ccg-esb-lab/BAFFLE/data/Figure_gradient/gradMontage_small.png

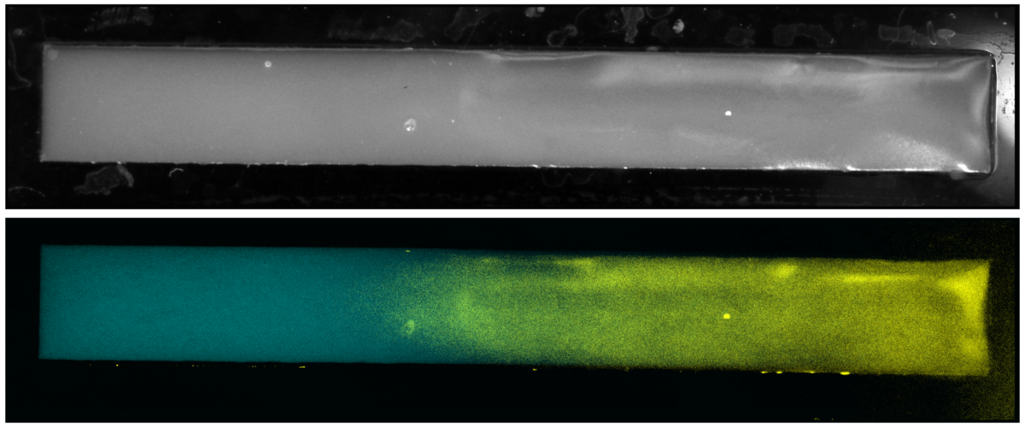
data/Figure_gradient/gradMontage_small.png
