ccg-esb-lab/BAFFLE/data/Figure_gradient/gradComposite.png

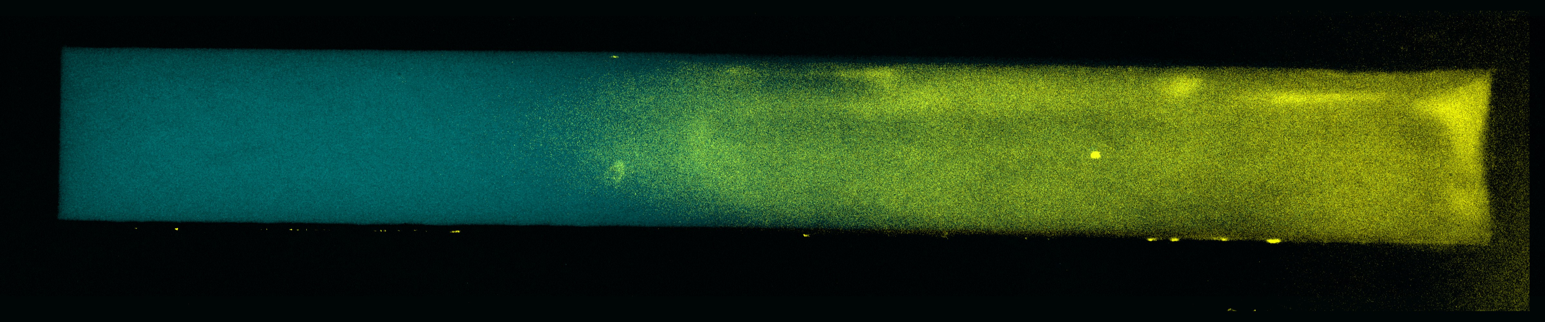
data/Figure_gradient/gradComposite.png
