ccg-esb-lab/BAFFLE/data/Figure_colonies/IMG_0024.JPG

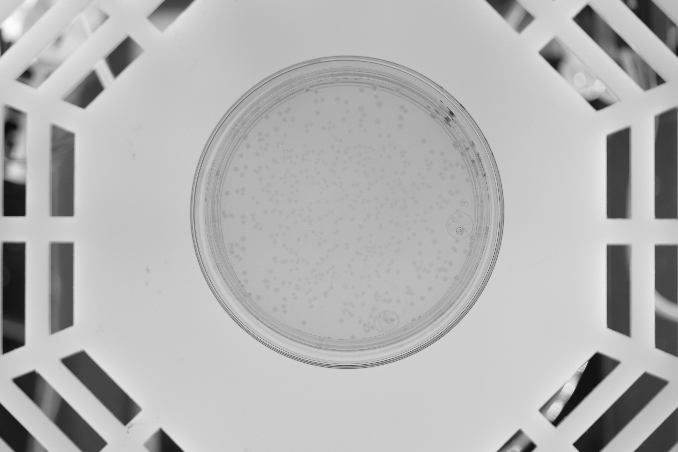
data/Figure_colonies/IMG_0024.JPG
