ccg-esb-lab/BAFFLE/data/Figure_colonies/IMG_0025.JPG

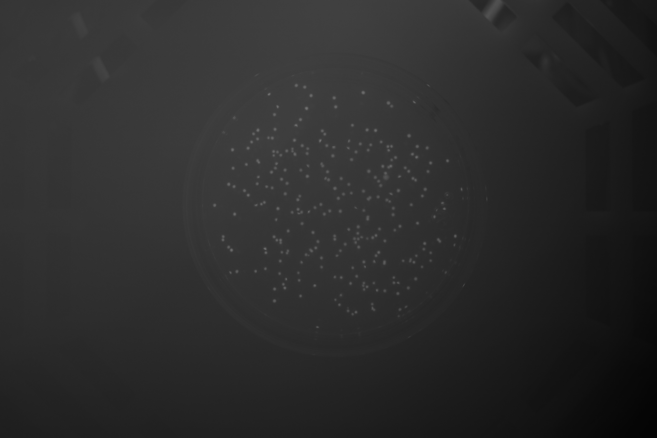
data/Figure_colonies/IMG_0025.JPG
