ccg-esb-lab/BAFFLE/data/Figure_colonies/IMG_0036.JPG

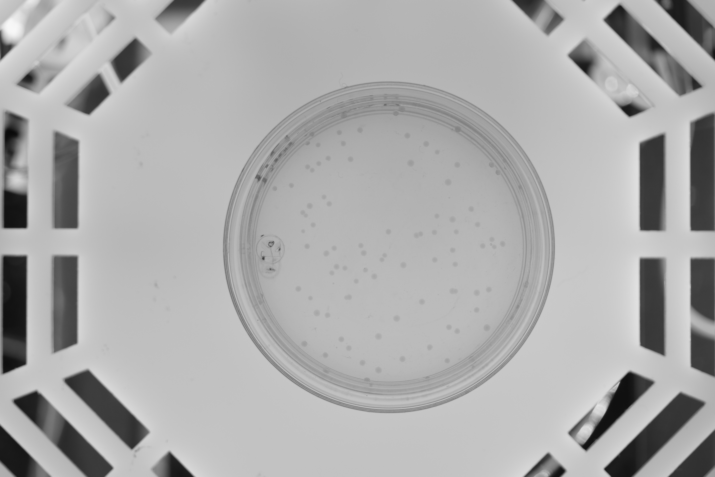
data/Figure_colonies/IMG_0036.JPG
