ccg-esb-lab/BAFFLE/data/Figure_colonies/IMG_0049.JPG

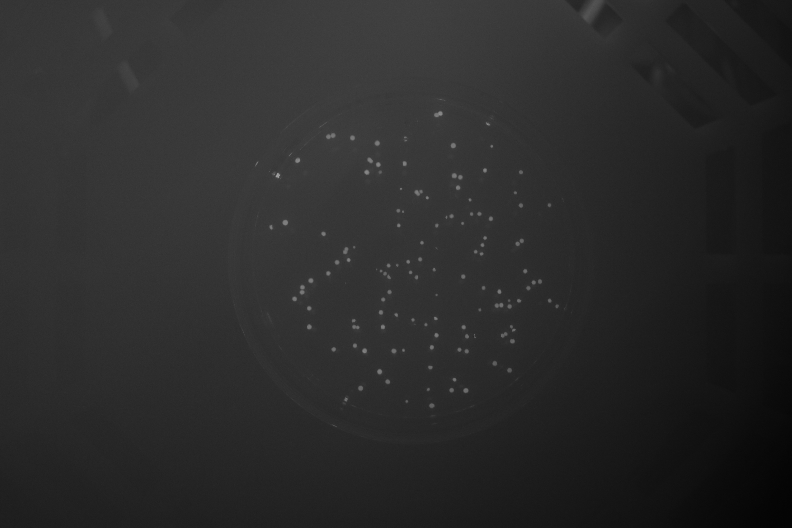
data/Figure_colonies/IMG_0049.JPG
