ccg-esb-lab/BAFFLE/data/Figure_colonies/IMG_0213.JPG

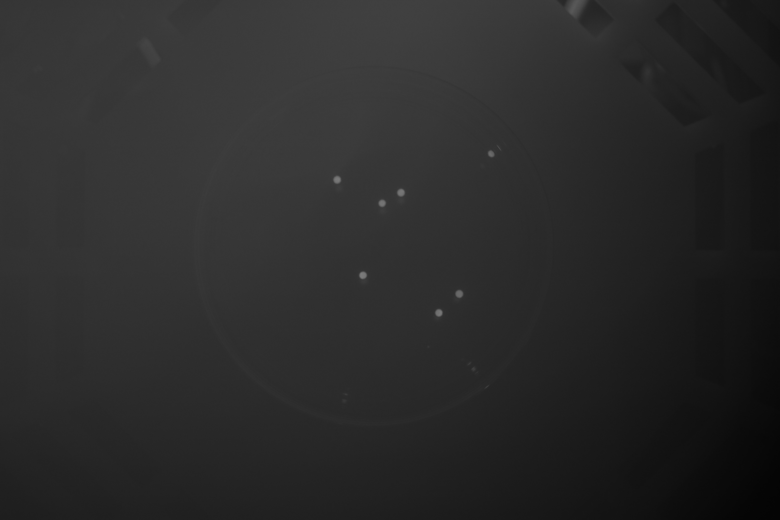
data/Figure_colonies/IMG_0213.JPG
