ccg-esb-lab/BAFFLE/data/Figure_colonies/IMG_0228.JPG

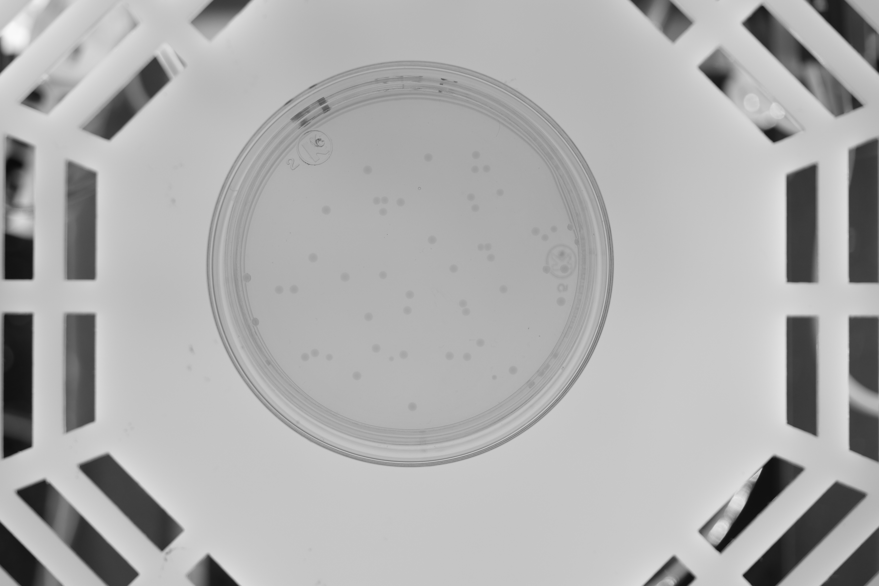
data/Figure_colonies/IMG_0228.JPG
