ccg-esb-lab/BAFFLE/data/Figure_gradient/gradCYAN.png

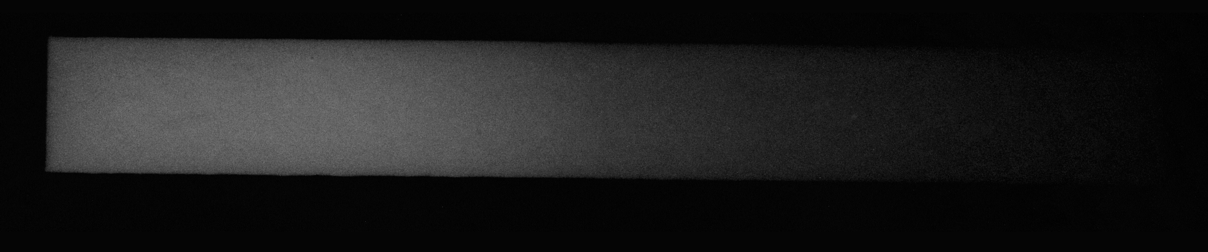
data/Figure_gradient/gradCYAN.png
