ccg-esb-lab/BAFFLE/data/Figure_gradient/gradDARK.png

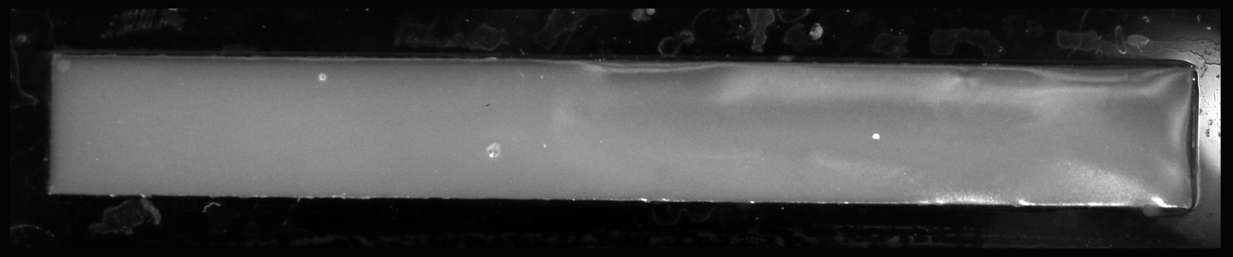
data/Figure_gradient/gradDARK.png
