ccg-esb-lab/BAFFLE/data/Figure_gradient/gradYELL.png

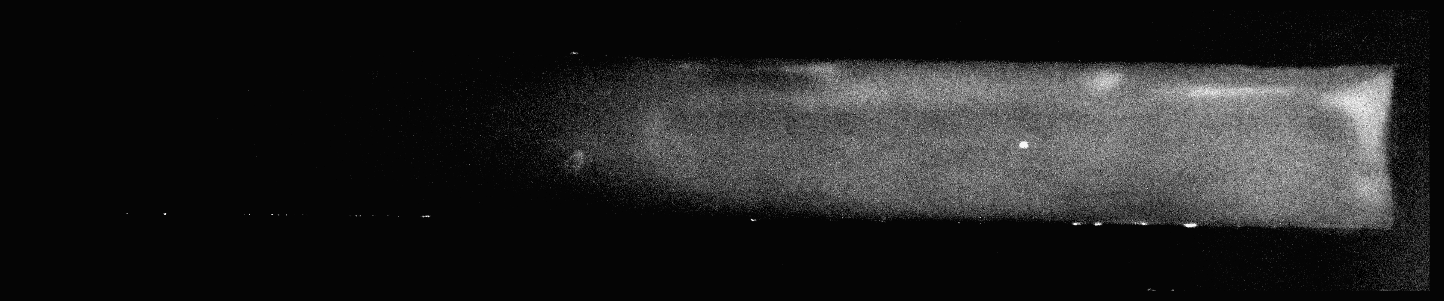
data/Figure_gradient/gradYELL.png
