ccg-esb-lab/BAFFLE/design_files/v3.2/STL/filter_wheel_shaft_spacer.stl

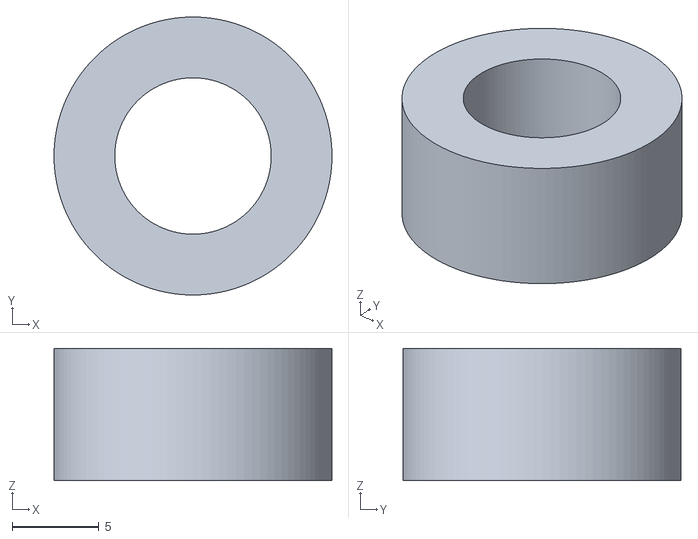
[picture p27: CAD file, 2020-06-24]
design_files/v3.2/STL/filter_wheel_shaft_spacer.stl
16.0 x 16.0 x 7.60
