ccg-esb-lab/BAFFLE/design_files/v3.2/STL/incubator_illuminator_support.stl

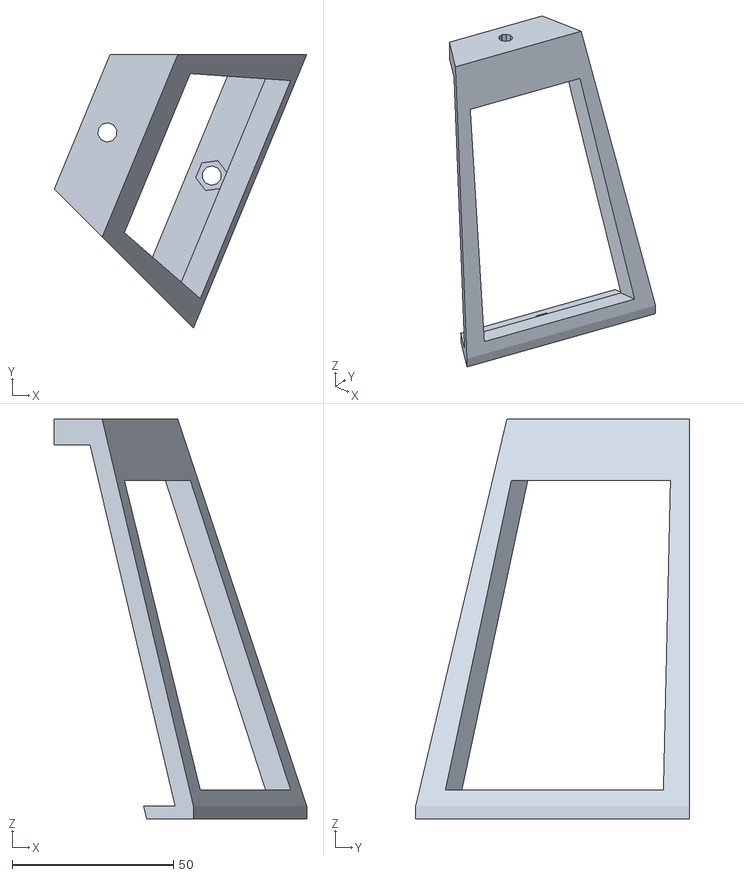
[picture p28: CAD file, 2020-06-24]
design_files/v3.2/STL/incubator_illuminator_support.stl
78.3 x 84.9 x 124.0
