ccg-esb-lab/BAFFLE/data/Figure_calibration/overlay_montage.png

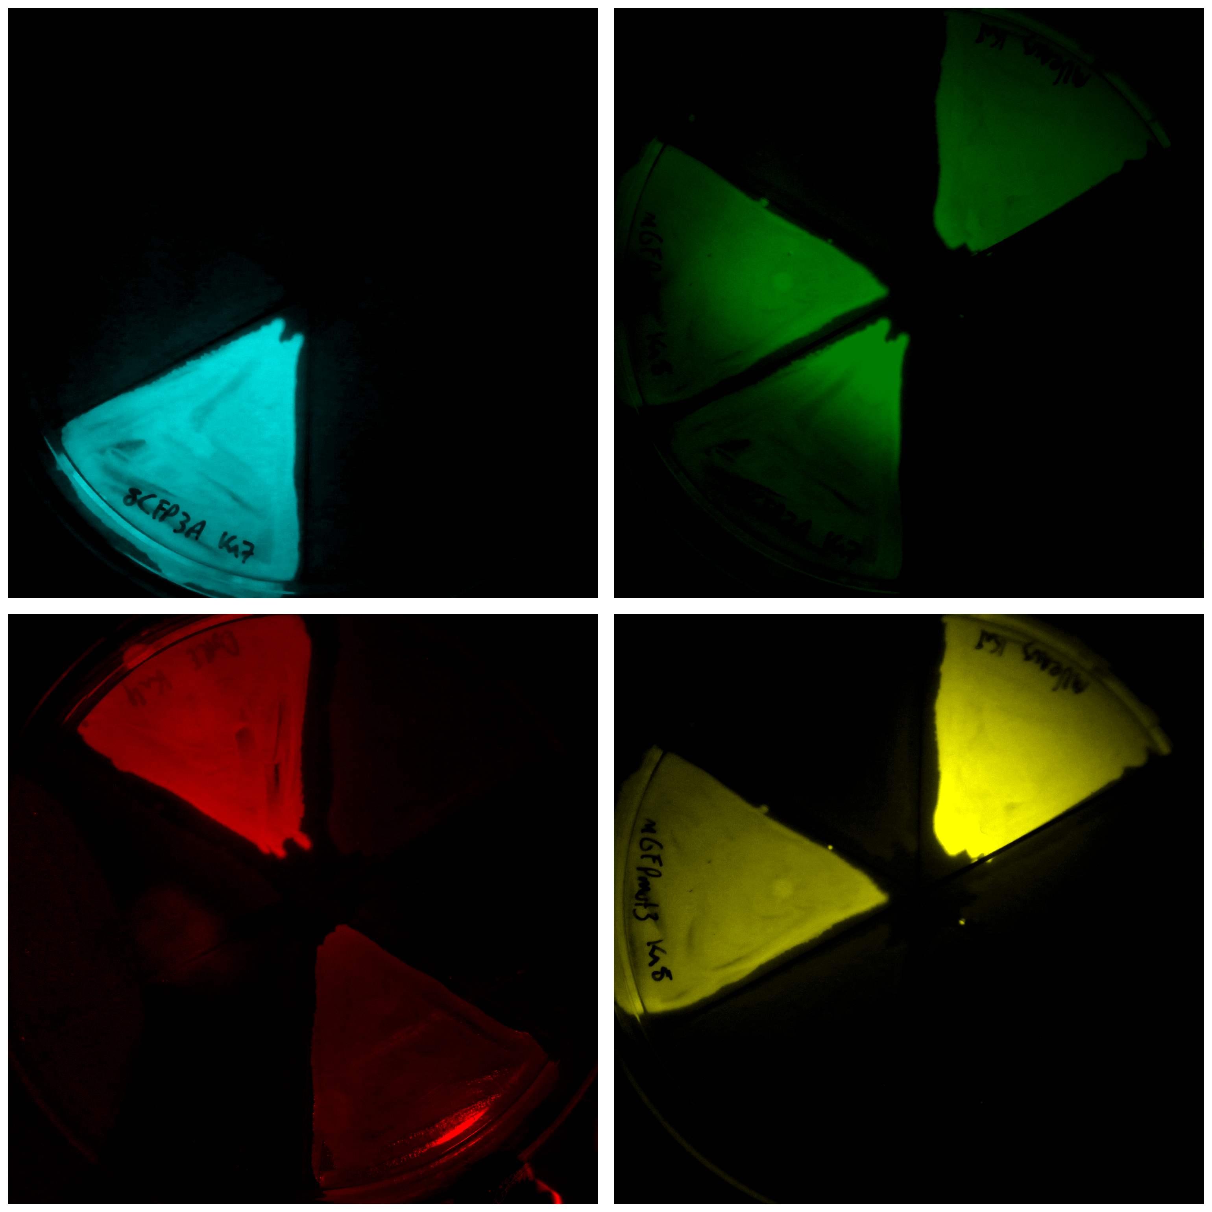
data/Figure_calibration/overlay_montage.png
