ccg-esb-lab/BAFFLE/data/Figure_gradient/gradMontageOverlay_small.png

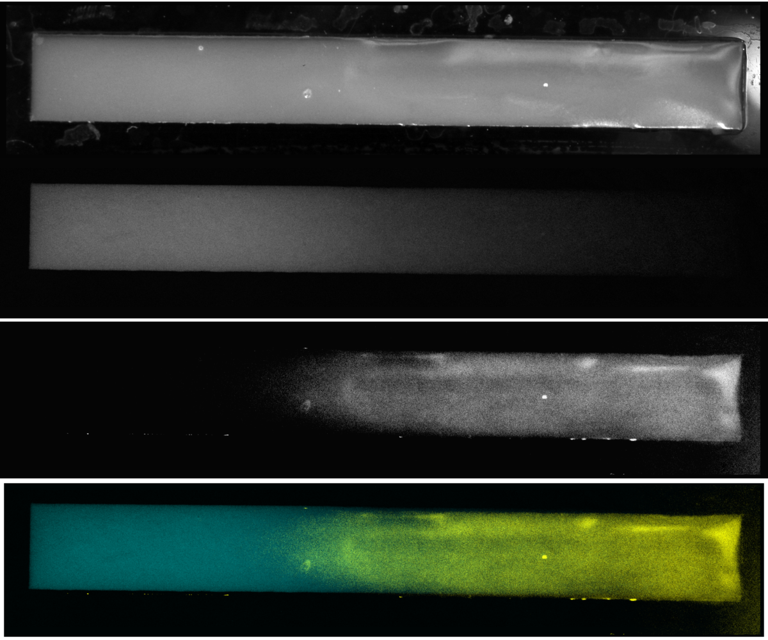
data/Figure_gradient/gradMontageOverlay_small.png
