ccg-esb-lab/BAFFLE/data/Figure_expansion/DATA/Results_RFP.csv

 | Label | Area | Mean | Min | Max | XM | YM | BX | BY | Width | Height | IntDen | RawIntDen | Slice
1 | RFP | 316 | 122.4525 | 104 | 132 | 1819.9500 | 1819.9893 | 1810 | 1810 | 20 | 20 | 38695.0000 | 38695.0000 | 1
2 | RFP | 948 | 121.6973 | 108 | 133 | 1819.8204 | 1819.9484 | 1800 | 1800 | 40 | 40 | 115369.0000 | 115369.0000 | 1
3 | RFP | 1564 | 121.4584 | 107 | 133 | 1819.5742 | 1820.0102 | 1790 | 1790 | 60 | 60 | 189961.0000 | 189961.0000 | 1
4 | RFP | 2196 | 121.6521 | 101 | 138 | 1819.1105 | 1820.0872 | 1780 | 1780 | 80 | 80 | 267148.0000 | 267148.0000 | 1
5 | RFP | 2836 | 122.4845 | 95 | 142 | 1818.4677 | 1820.1432 | 1770 | 1770 | 100 | 100 | 347366.0000 | 347366.0000 | 1
6 | RFP | 3444 | 123.4463 | 104 | 145 | 1817.9614 | 1820.3368 | 1760 | 1760 | 120 | 120 | 425149.0000 | 425149.0000 | 1
7 | RFP | 4076 | 125.0353 | 104 | 147 | 1817.2078 | 1820.5984 | 1750 | 1750 | 140 | 140 | 509644.0000 | 509644.0000 | 1
8 | RFP | 4728 | 126.8976 | 102 | 150 | 1816.3746 | 1820.8696 | 1740 | 1740 | 160 | 160 | 599972.0000 | 599972.0000 | 1
9 | RFP | 5340 | 128.7163 | 99 | 153 | 1815.3119 | 1821.2253 | 1730 | 1730 | 180 | 180 | 687345.0000 | 687345.0000 | 1
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
