ccg-esb-lab/BAFFLE/data/Figure_calibration/bg_DARK.jpg

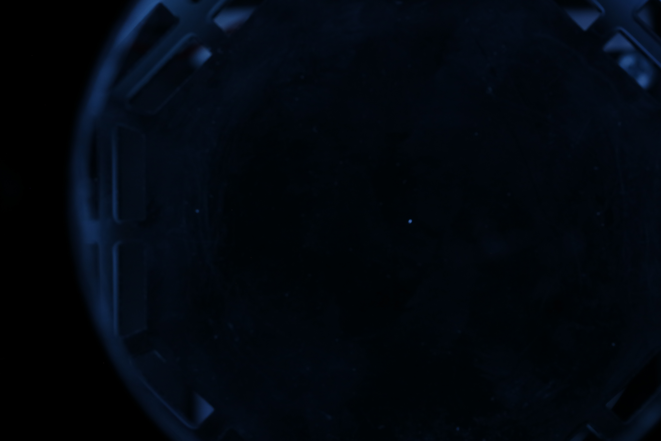
data/Figure_calibration/bg_DARK.jpg
