ccg-esb-lab/BAFFLE/data/Figure_calibration/bg_YFP.jpg

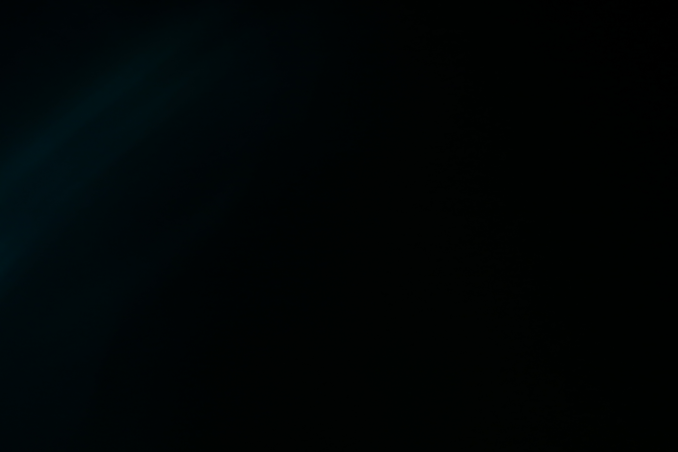
data/Figure_calibration/bg_YFP.jpg
