ccg-esb-lab/BAFFLE/data/Figure_calibration/overlay_CFP.png

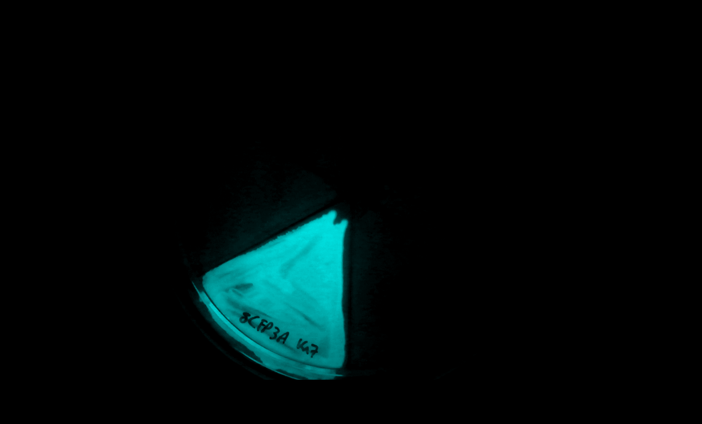
data/Figure_calibration/overlay_CFP.png
