ccg-esb-lab/BAFFLE/data/Figure_calibration/plate_CFP.jpg

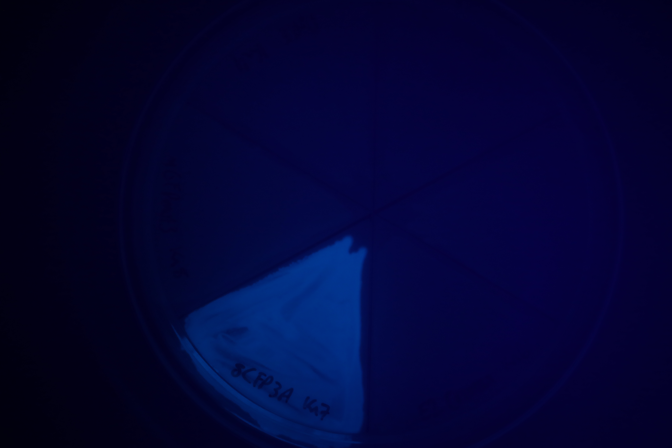
data/Figure_calibration/plate_CFP.jpg
