ccg-esb-lab/BAFFLE/data/Figure_calibration/plate_YFP.jpg

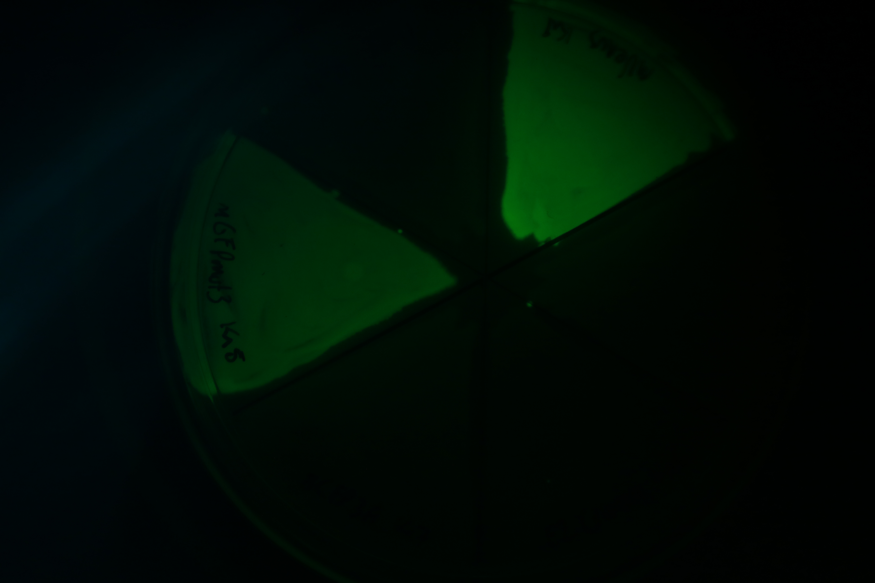
data/Figure_calibration/plate_YFP.jpg
